telekom-security/tpotmobile/images/map_476320.png

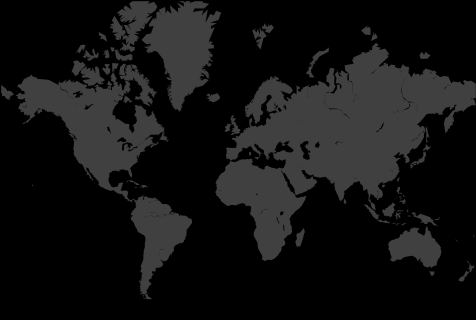
images/map_476320.png
