telekom-security/tpotmobile/images/map_800477.png

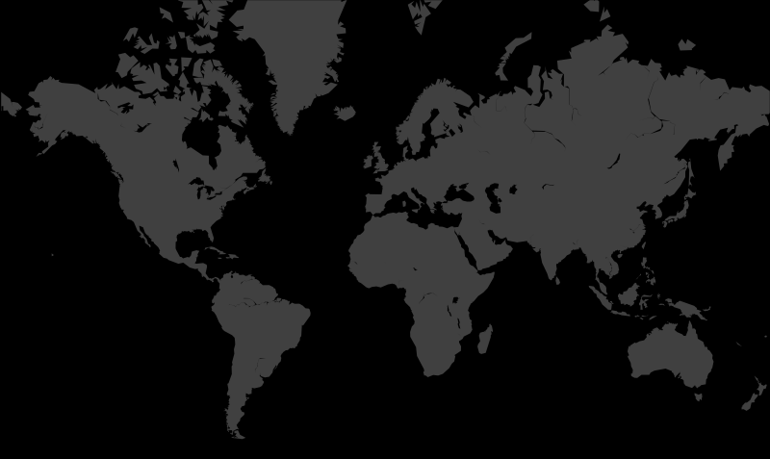
images/map_800477.png
