telekom-security/tpotmobile/images/tpot_480320.png

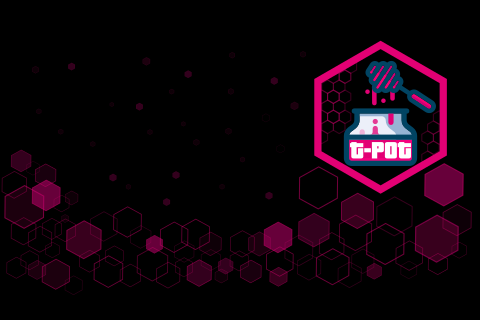
images/tpot_480320.png
