telekom-security/tpotmobile/images/tpot_800480.png

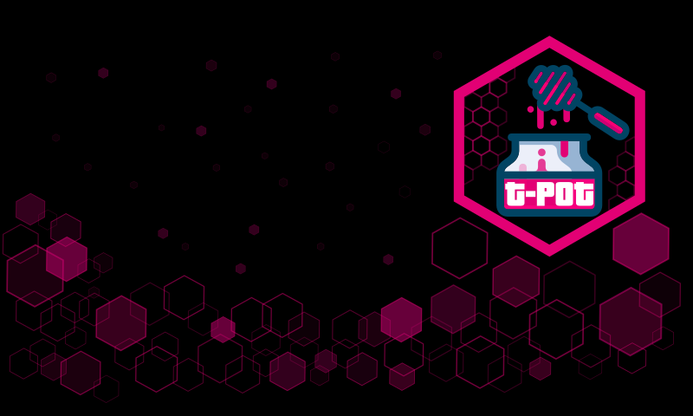
images/tpot_800480.png
