telekom-security/tpotmobile/images/tpot_1280800.png

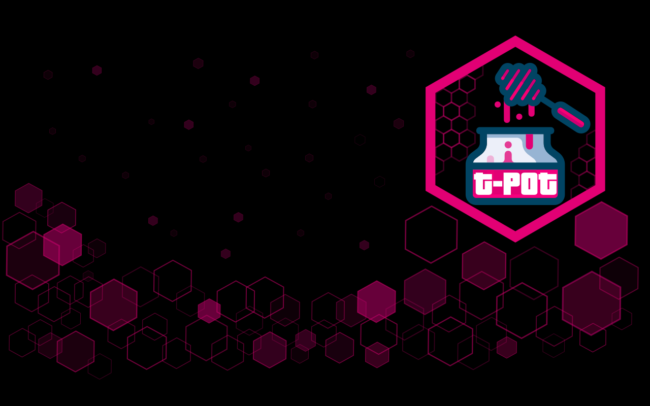
images/tpot_1280800.png
