telekom-security/tpotmobile/screenshots/8inch/build28.jpg

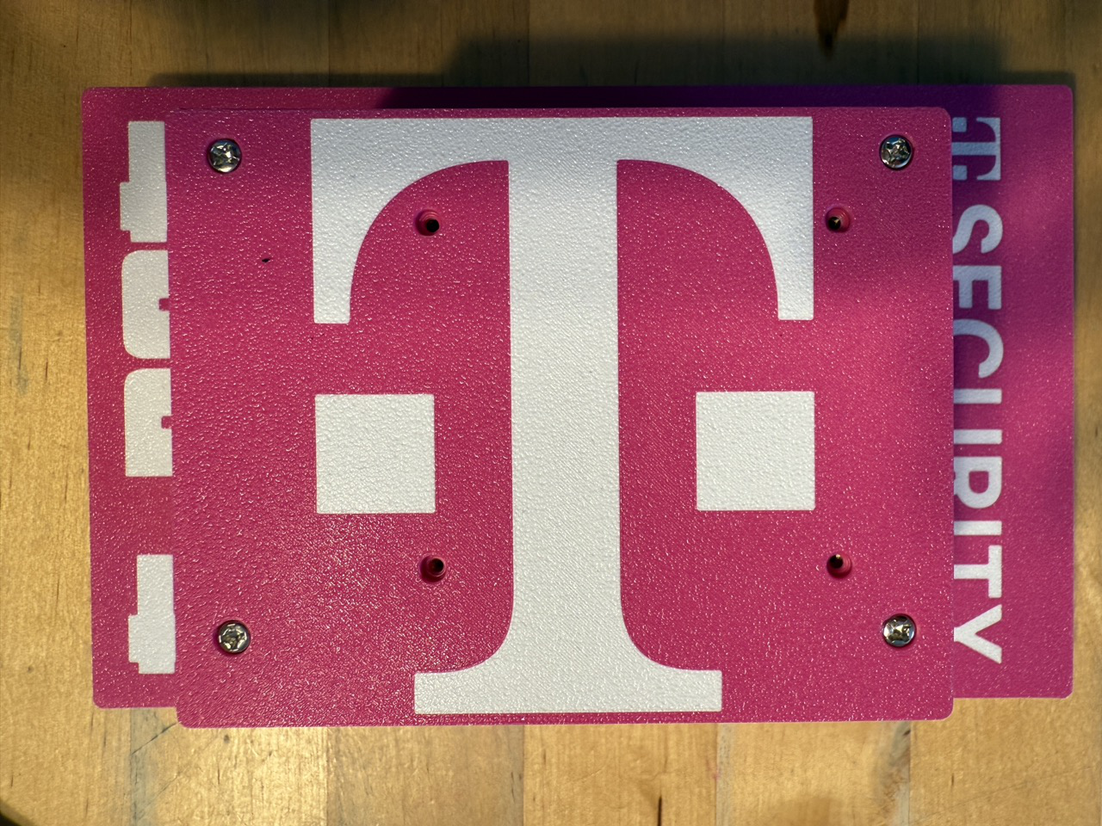
screenshots/8inch/build28.jpg
