telekom-security/tpotmobile/screenshots/8inch/build29.jpg

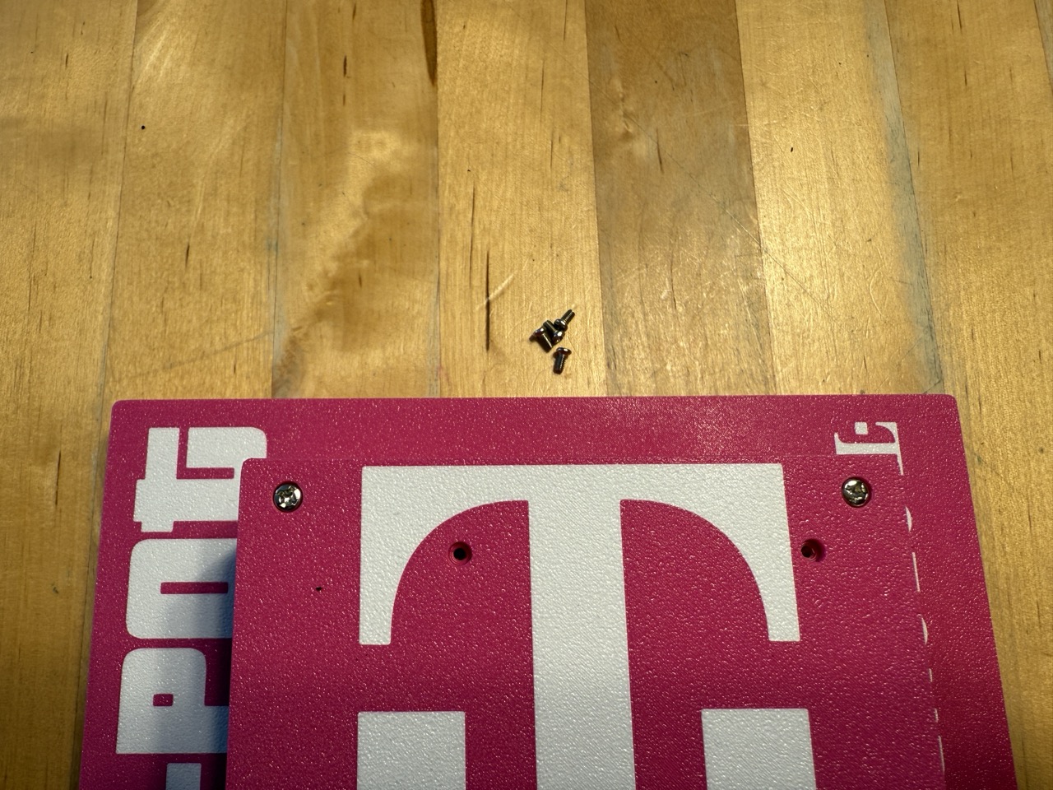
screenshots/8inch/build29.jpg
